khaled147/Koneked/Koneked_Case/Nano33BLE_Stock/Nano33BLEback.png

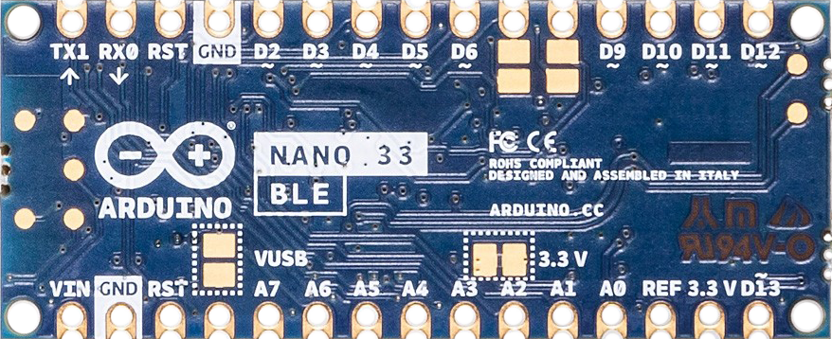
Koneked_Case/Nano33BLE_Stock/Nano33BLEback.png
