khaled147/Koneked/Koneked_Case/Nano33BLE_Stock/Nano33BLEbackPerspective.png

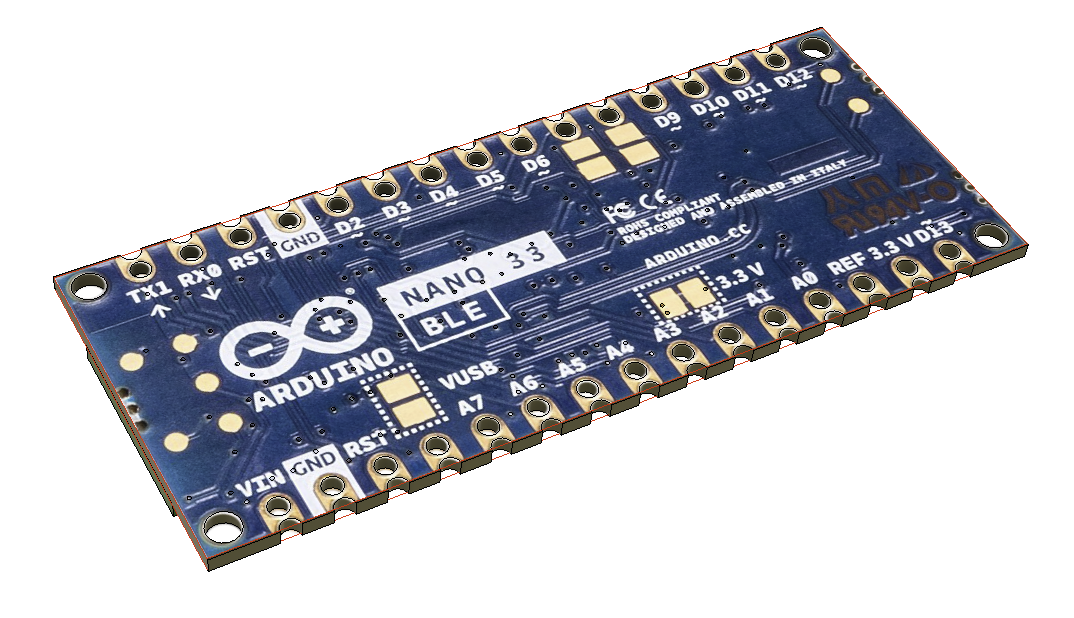
Koneked_Case/Nano33BLE_Stock/Nano33BLEbackPerspective.png
