khaled147/Koneked/Koneked_Case/Other/Koneked_PWR_Daughter_Circuit.png

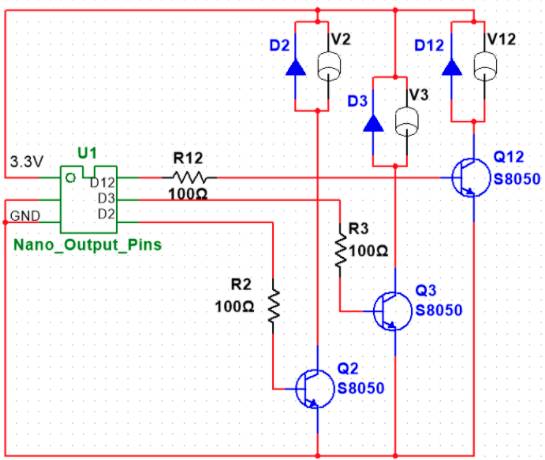
Koneked_Case/Other/Koneked_PWR_Daughter_Circuit.png
