khaled147/Koneked/Koneked_Case/Other/Koneked_X.JPG

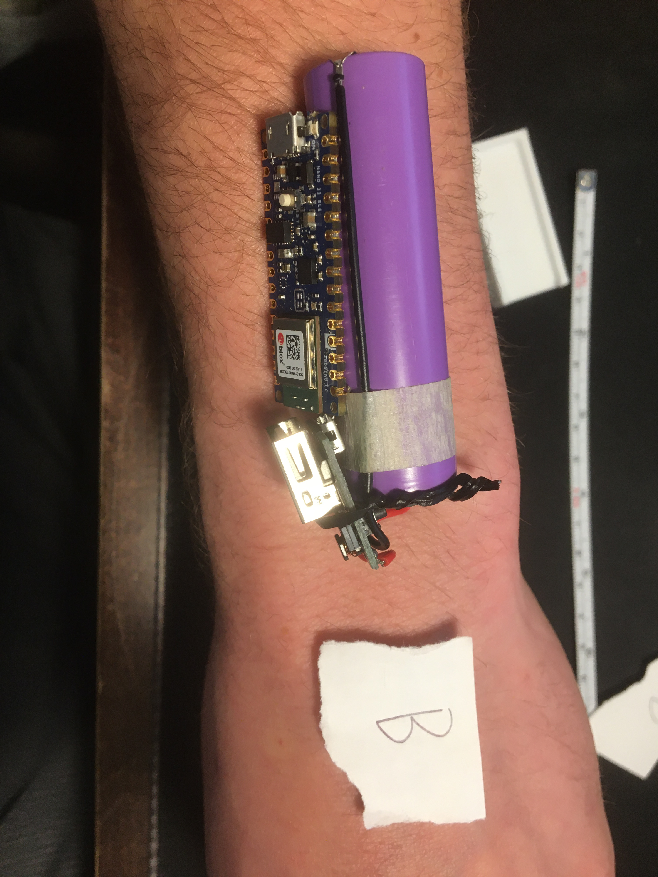
Koneked_Case/Other/Koneked_X.JPG
