khaled147/Koneked/Koneked_Case/Other/Koneked_Y.JPG

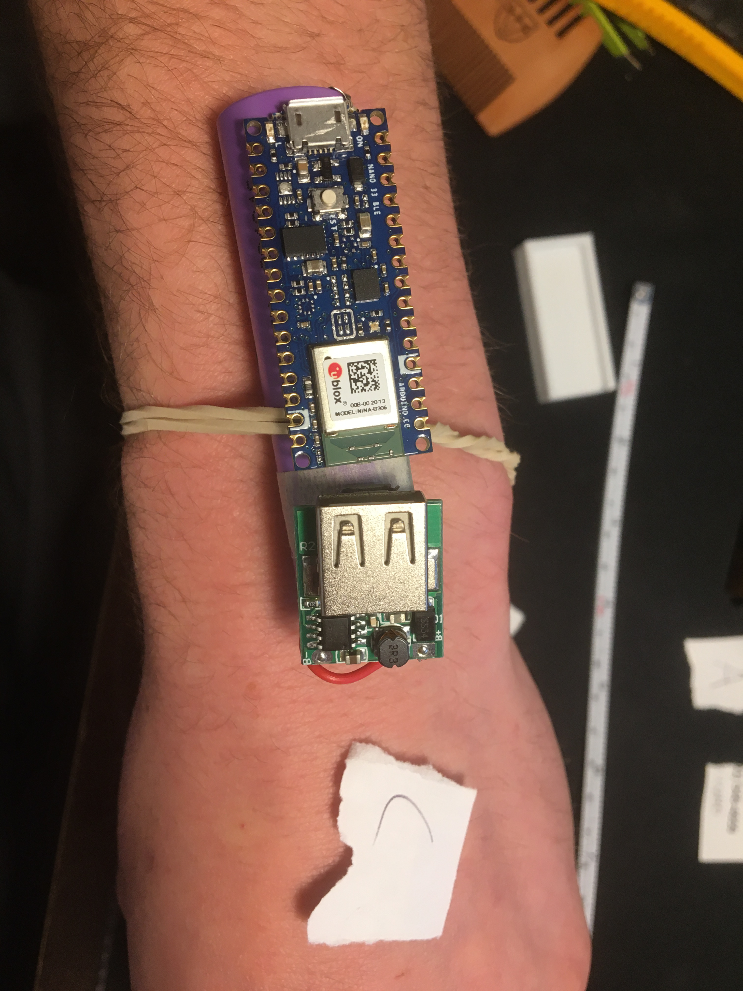
Koneked_Case/Other/Koneked_Y.JPG
