khaled147/Koneked/Koneked_Case/Other/Koneked_Z.JPG

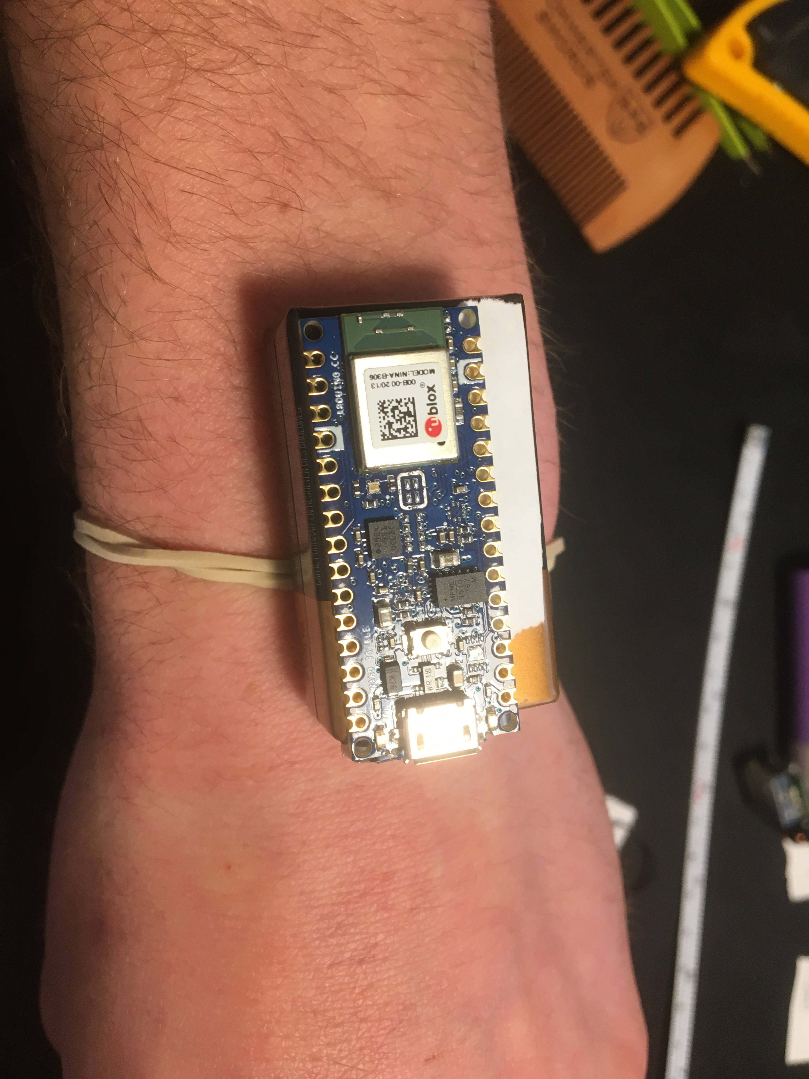
Koneked_Case/Other/Koneked_Z.JPG
