khaled147/Koneked/Arduino/Tensorflow_Model/Nano33ble_voice_classifier/Nano33ble_voice_classifier.ino

/*
 * Voice classifier for Arduino Nano 33 BLE Sense by Alan Wang
 */

#include <math.h>
#include <PDM.h>
#include <EloquentTinyML.h>      // https://github.com/eloquentarduino/EloquentTinyML
#include "tf_lite_model.h"       // TF Lite model file


#define PDM_SOUND_GAIN     255   // sound gain of PDM mic
#define PDM_BUFFER_SIZE    256   // buffer size of PDM mic

#define SAMPLE_THRESHOLD   900   // RMS threshold to trigger sampling
#define FEATURE_SIZE       32    // sampling size of one voice instance
#define SAMPLE_DELAY       20    // delay time (ms) between sampling

#define NUMBER_OF_LABELS   3     // number of voice labels
const String words[NUMBER_OF_LABELS] = {"Yes", "No", "OK"};  // words for each label


#define PREDIC_THRESHOLD   0.6   // prediction probability threshold for labels
#define RAW_OUTPUT         true  // output prediction probability of each label
#define NUMBER_OF_INPUTS   FEATURE_SIZE
#define NUMBER_OF_OUTPUTS  NUMBER_OF_LABELS
#define TENSOR_ARENA_SIZE  4 * 1024


Eloquent::TinyML::TfLite<NUMBER_OF_INPUTS, NUMBER_OF_OUTPUTS, TENSOR_ARENA_SIZE> tf_model;
float feature_data[FEATURE_SIZE];
volatile float rms;
bool voice_detected;


// callback function for PDM mic
void onPDMdata() {

  rms = -1;
  short sample_buffer[PDM_BUFFER_SIZE];
  int bytes_available = PDM.available();
  PDM.read(sample_buffer, bytes_available);

  // calculate RMS (root mean square) from sample_buffer
  unsigned int sum = 0;
  for (unsigned short i = 0; i < (bytes_available / 2); i++) sum += pow(sample_buffer[i], 2);
  rms = sqrt(float(sum) / (float(bytes_available) / 2.0));
}

void setup() {

  Serial.begin(115200);
  while (!Serial);

  PDM.onReceive(onPDMdata);
  PDM.setBufferSize(PDM_BUFFER_SIZE);
  PDM.setGain(PDM_SOUND_GAIN);

  if (!PDM.begin(1, 16000)) {  // start PDM mic and sampling at 16 KHz
    Serial.println("Failed to start PDM!");
    while (1);
  }

  pinMode(LED_BUILTIN, OUTPUT);

  // wait 1 second to avoid initial PDM reading
  delay(900);
  digitalWrite(LED_BUILTIN, HIGH);
  delay(100);
  digitalWrite(LED_BUILTIN, LOW);

  // start TF Lite model
  tf_model.begin((unsigned char*) model_data);
  
  Serial.println("=== Classifier start ===\n");
}

void loop() {

  // waiting until sampling triggered
  while (rms < SAMPLE_THRESHOLD);

  digitalWrite(LED_BUILTIN, HIGH);
  for (int i = 0; i < FEATURE_SIZE; i++) {  // sampling
    while (rms < 0);
    feature_data[i] = rms;
    delay(SAMPLE_DELAY);
  }
  digitalWrite(LED_BUILTIN, LOW);

  // predict voice and put results (probability) for each label in the array
  float prediction[NUMBER_OF_LABELS];
  tf_model.predict(feature_data, prediction);

  // print out prediction results;
  // in theory, you need to find the highest probability in the array,
  // but only one of them would be high enough over 0.5~0.6
  Serial.println("Predicting the word:");
  if (RAW_OUTPUT) {
    for (int i = 0; i < NUMBER_OF_LABELS; i++) {
      Serial.print("Label ");
      Serial.print(i);
      Serial.print(" = ");
      Serial.println(prediction[i]);
    }
  }
  voice_detected = false;
  for (int i = 0; i < NUMBER_OF_LABELS; i++) {
    if (prediction[i] >= PREDIC_THRESHOLD) {
      Serial.print("Word detected: ");
      Serial.println(words[i]);
      Serial.println("");
      voice_detected = true;
    }
  }
  if (!voice_detected && !RAW_OUTPUT) Serial.println("Word not recognized\n");

  // wait for 1 second after one sampling/prediction
  delay(900);
  digitalWrite(LED_BUILTIN, HIGH);
  delay(100);
  digitalWrite(LED_BUILTIN, LOW);
}
