khaled147/Koneked/Arduino/Tensorflow_Model_2/arduino-33-ble-sense-classify-audio/Classifier.h

#pragma once
#include <cstdarg>
namespace Eloquent {
    namespace ML {
        namespace Port {
            class SVM {
                public:
                    /**
                    * Predict class for features vector
                    */
                    int predict(float *x) {
                        float kernels[79] = { 0 };
                        float decisions[3] = { 0 };
                        int votes[3] = { 0 };
                        kernels[0] = compute_kernel(x,   32.779999  , 38.139999  , 40.459999  , 41.579998  , 40.459999  , 39.32  , 35.279999  , 34.34  , 33.959999  , 36.380001  , 35.099998  , 34.139999  , 34.899998  , 38.98  , 30.699999  , 19.82  , 17.359999  , 20.139999  , 25.599998  , 23.18  , 22.02  , 16.98  , 12.54  , 10.219999  , 5.1  , 0.0  , 0.0  , 3.62  , 9.559999  , 13.04  , 16.58  , 19.48  , 22.02  , 22.879999  , 24.0  , 22.299999  , 21.4  , 21.719999  , 21.4  , 19.48  , 18.459999  , 17.719999  , 18.799999  , 17.359999  , 16.58  , 14.92  , 14.92  , 14.02  , 12.54  , 11.44  , 10.86  , 8.86  , 8.08  , 6.26  , 8.08  , 8.08  , 8.08  , 7.24  , 6.26  , 5.1  , 7.24  , 7.24  , 5.1  , 3.62 );
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
                        + kernels[73] * -1.3032866e-05
                        + kernels[74] * -1.9450036e-05
                        + kernels[77] * -5.5385819e-05
                        + kernels[78] * -2.0520587e-05
                        ;
                        decisions[2] = -1.384387558751
                        + kernels[31] * 4.3153716e-05
                        + kernels[35] * 2.855534e-06
                        + kernels[36] * 0.000143355834
                        + kernels[37] * 1.321356e-06
                        + kernels[38] * 0.000140003562
                        + kernels[39] * 2.1155889e-05
                        + kernels[41] * 8.403057e-06
                        + kernels[44] * 0.000134274662
                        + kernels[45] * 3.63022e-07
                        + kernels[51] * 1.447636e-06
                        + kernels[53] * 8.14144e-07
                        + kernels[55] * -1.667008e-06
                        + kernels[56] * -4.083557e-06
                        + kernels[58] * -2.88931e-06
                        + kernels[59] * -4.351462e-06
                        + kernels[60] * -1.259603e-06
                        + kernels[62] * -0.000202344274
                        + kernels[63] * -6.01004e-07
                        + kernels[64] * -3.1183036e-05
                        + kernels[67] * -1.4385832e-05
                        + kernels[69] * -2.2281455e-05
                        + kernels[70] * -2.462854e-06
                        + kernels[71] * -1.0439618e-05
                        + kernels[72] * -6.008427e-06
                        + kernels[73] * -1.1087063e-05
                        + kernels[74] * -0.000146482662
                        + kernels[75] * -6.798756e-06
                        + kernels[76] * -1.576243e-05
                        + kernels[77] * -5.275662e-06
                        + kernels[78] * -7.7844e-06
                        ;
                        votes[decisions[0] > 0 ? 0 : 1] += 1;
                        votes[decisions[1] > 0 ? 0 : 2] += 1;
                        votes[decisions[2] > 0 ? 1 : 2] += 1;
                        int val = votes[0];
                        int idx = 0;

                        for (int i = 1; i < 3; i++) {
                            if (votes[i] > val) {
                                val = votes[i];
                                idx = i;
                            }
                        }

                        return idx;
                    }

                    /**
                    * Predict readable class name
                    */
                    const char* predictLabel(float *x) {
                        return idxToLabel(predict(x));
                    }

                    /**
                    * Convert class idx to readable name
                    */
                    const char* idxToLabel(uint8_t classIdx) {
                        switch (classIdx) {
                            case 0:
                            return "bye";
                            case 1:
                            return "hello";
                            case 2:
                            return "yes";
                            default:
                            return "Houston we have a problem";
                        }
                    }

                protected:
                    /**
                    * Compute kernel between feature vector and support vector.
                    * Kernel type: poly
                    */
                    float compute_kernel(float *x, ...) {
                        va_list w;
                        va_start(w, 64);
                        float kernel = 0.0;

                        for (uint16_t i = 0; i < 64; i++) {
                            kernel += x[i] * va_arg(w, double);
                        }

                        return pow((0.1 * kernel) + 0.0, 2);
                    }
                };
            }
        }
    }
